yang300100/LifeLog/prototype/e2e_output/annotated_20260630_160411.png

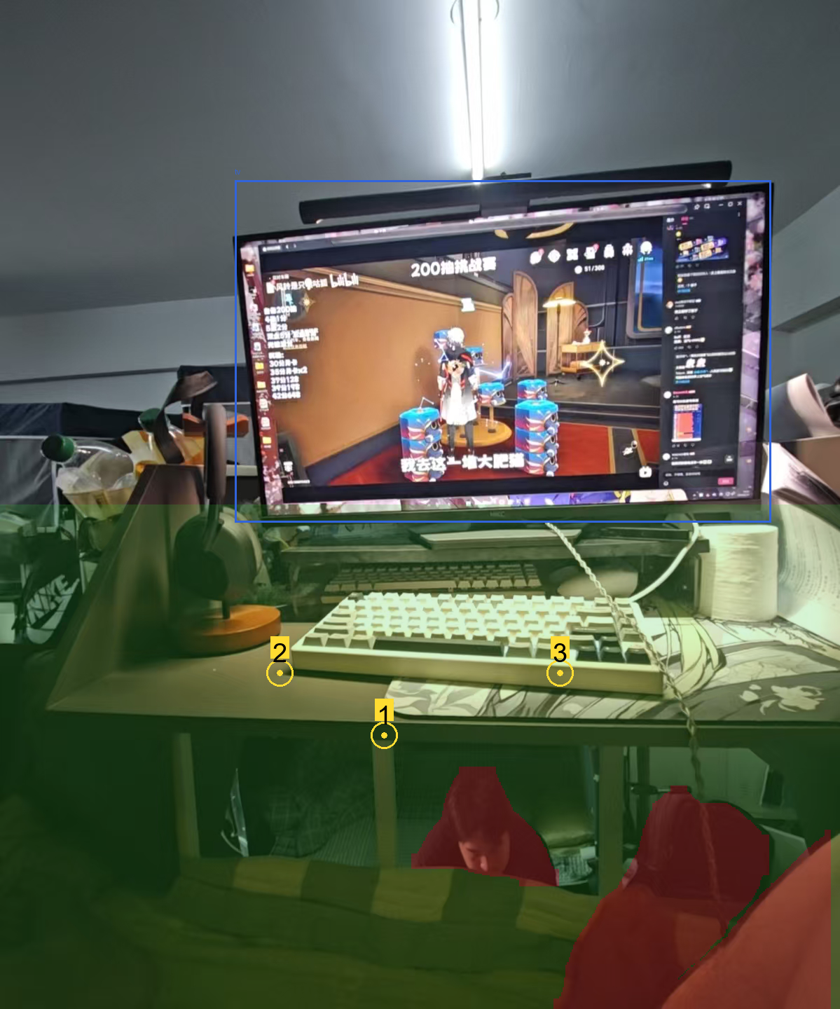
prototype/e2e_output/annotated_20260630_160411.png
