yang300100/LifeLog/prototype/output/01_character_raw.png

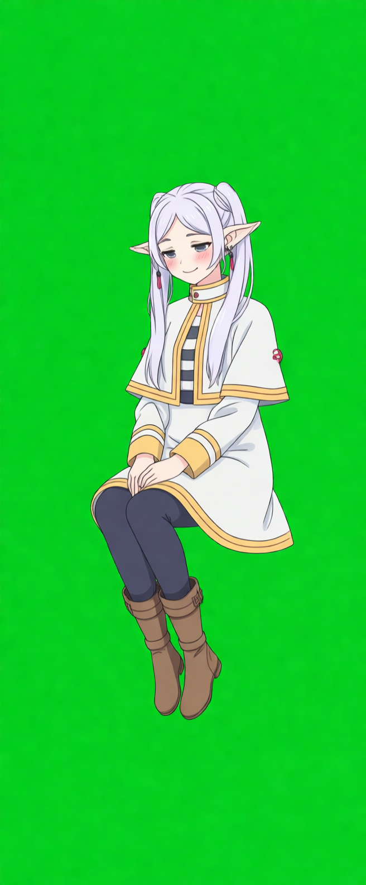
prototype/output/01_character_raw.png
