yang300100/LifeLog/prototype/output/02_character_nobg.png

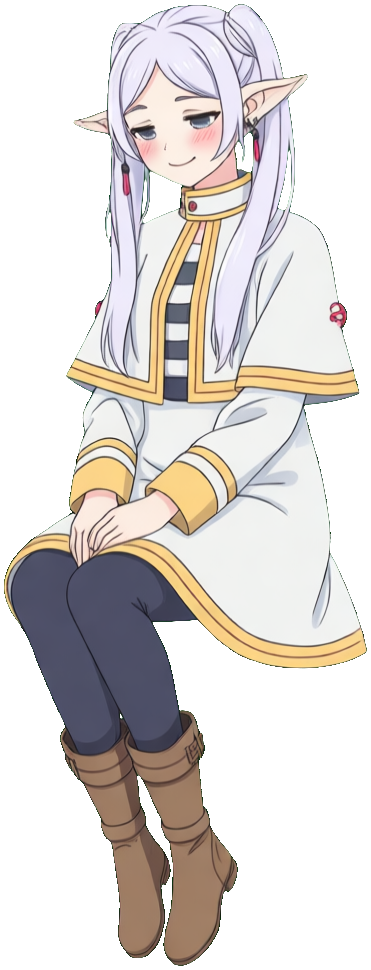
prototype/output/02_character_nobg.png
