yang300100/LifeLog/prototype/ref_01.png

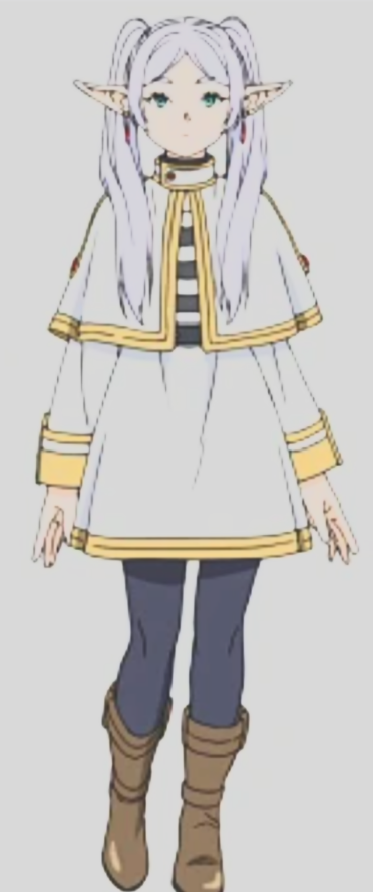
prototype/ref_01.png
