yang300100/LifeLog/prototype/seedream_output/showcase_A_standing_20260630_153909.png

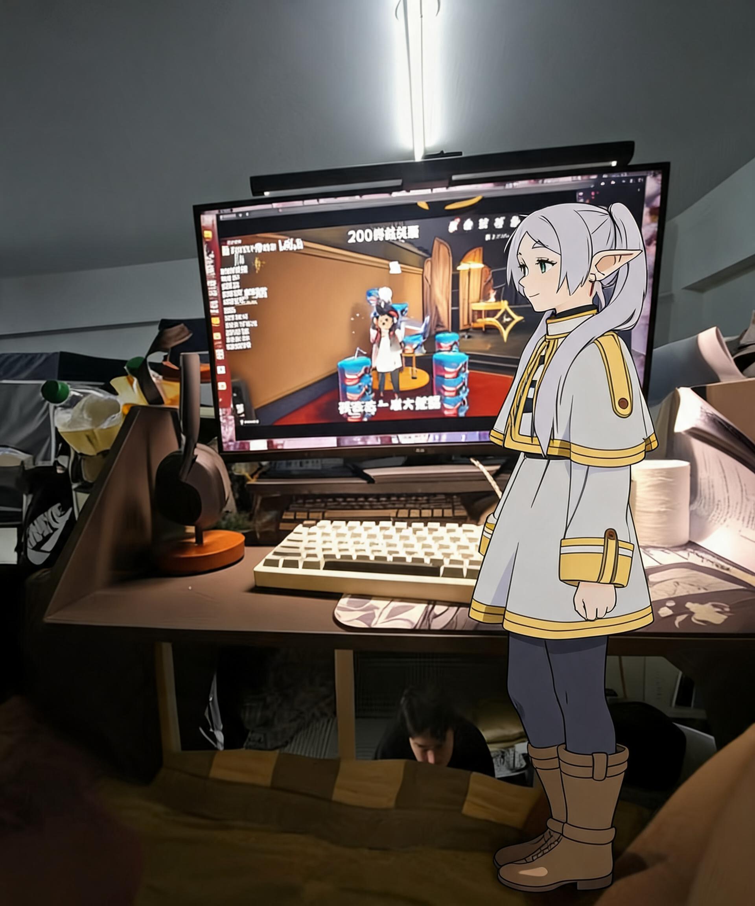
prototype/seedream_output/showcase_A_standing_20260630_153909.png
