yang300100/LifeLog/prototype/seedream_output/showcase_C_lean_forward_20260630_154052.png

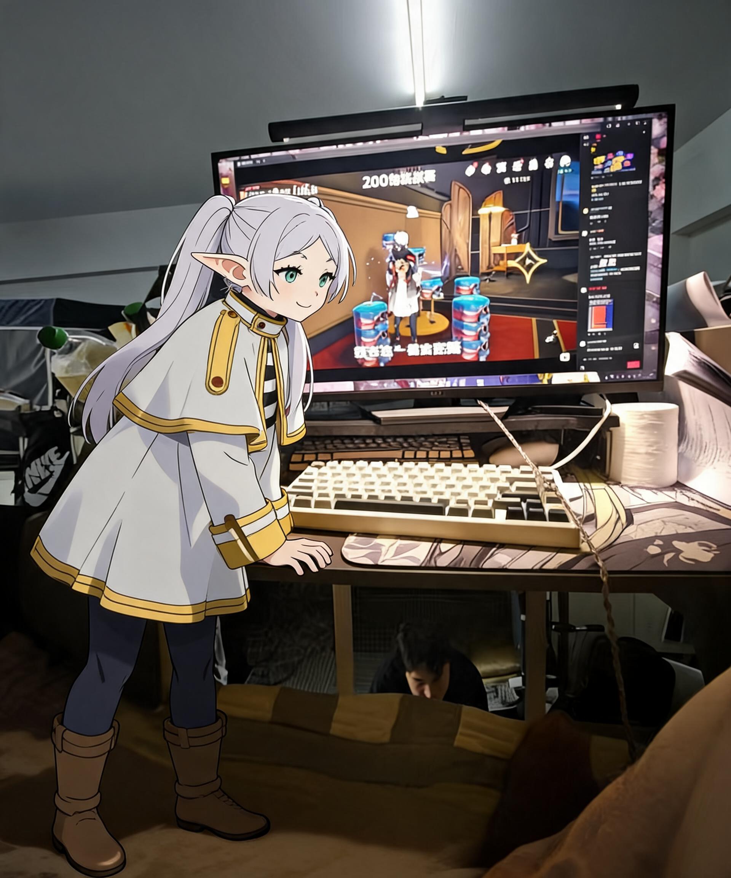
prototype/seedream_output/showcase_C_lean_forward_20260630_154052.png
