yang300100/LifeLog/prototype/e2e_output/final_result_20260630_160916.png

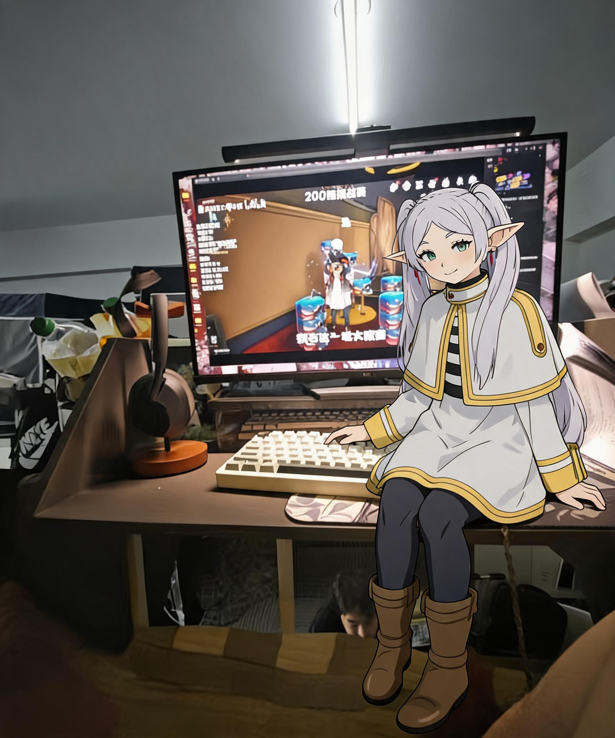
prototype/e2e_output/final_result_20260630_160916.png
