yang300100/LifeLog/prototype/test_scene.jpg

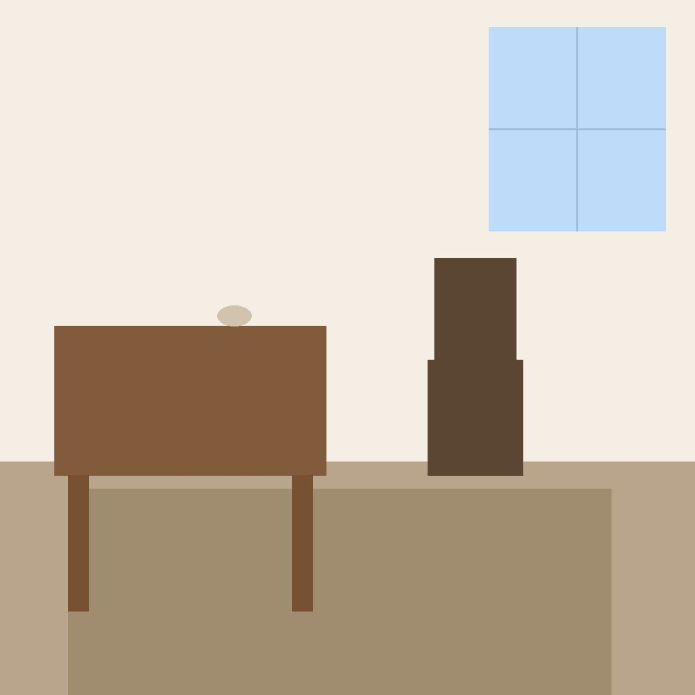
prototype/test_scene.jpg
