yang300100/LifeLog/firmware/lifelog/configuration.cpp

#include <Arduino.h>
#include "configuration.h"
#include "config.h"
#include "esp_camera.h"
#include <stdio.h>
#include <string.h>

// 简单的 key=value 解析，跳过空白和注释行
static bool parse_line(const char *line, char *key, size_t key_sz,
                       char *value, size_t val_sz) {
    const char *p = line;
    while (*p == ' ' || *p == '\t') p++;
    if (*p == '#' || *p == '\0' || *p == '\n' || *p == '\r') return false;

    const char *k = p;
    while (*p && *p != '=' && *p != '\n' && *p != '\r') p++;
    size_t klen = p - k;
    // 去掉 key 末尾的空格（"video_quality " → "video_quality"）
    while (klen > 0 && (k[klen - 1] == ' ' || k[klen - 1] == '\t')) klen--;
    if (klen >= key_sz) klen = key_sz - 1;
    memcpy(key, k, klen);
    key[klen] = '\0';

    if (*p != '=') return false;
    p++;

    while (*p == ' ' || *p == '\t') p++;
    const char *v = p;
    while (*p && *p != '\n' && *p != '\r') p++;
    size_t vlen = p - v;
    // 去掉 value 末尾的空格和回车
    while (vlen > 0 && (v[vlen - 1] == ' ' || v[vlen - 1] == '\t' || v[vlen - 1] == '\r')) vlen--;
    if (vlen >= val_sz) vlen = val_sz - 1;
    memcpy(value, v, vlen);
    value[vlen] = '\0';

    return true;
}

void config_set_defaults(AppConfig &cfg) {
    strcpy(cfg.capture_mode, "video");
    cfg.video_duration = VIDEO_DURATION_DEFAULT;
    cfg.video_resolution = VIDEO_RESOLUTION_DEFAULT;
    cfg.video_quality = VIDEO_QUALITY_DEFAULT;
    cfg.video_fps = VIDEO_FPS_DEFAULT;
    cfg.sharpness = 1;      // 默认锐度 +1
    cfg.contrast  = 0;      // 默认对比度中性
    cfg.saturation = 0;     // 默认饱和度中性
    cfg.interval = INTERVAL_DEFAULT;
    cfg.flash_threshold = FLASH_DARK_THRESHOLD;
    cfg.ble_advertise_timeout = BLE_ADV_TIMEOUT_DEFAULT;
    strcpy(cfg.ble_device_name, BLE_DEVICE_NAME_DEFAULT);
    cfg.ble_adv_interval = BLE_ADV_INTERVAL_DEFAULT;
}

bool config_load(const char *filepath, AppConfig &cfg) {
    config_set_defaults(cfg);

    FILE *f = fopen(filepath, "r");
    if (!f) return false;  // 文件不存在，使用默认值

    char line[128];
    char key[64], value[64];

    while (fgets(line, sizeof(line), f)) {
        // 检测行截断：最后字符不是 \n 且不是 EOF
        size_t len = strlen(line);
        if (len > 0 && line[len - 1] != '\n' && !feof(f)) {
            // 跳过被截断的行的剩余部分
            int c;
            while ((c = fgetc(f)) != '\n' && c != EOF) {}
            continue;
        }
        if (!parse_line(line, key, sizeof(key), value, sizeof(value)))
            continue;

        if (strcmp(key, "capture_mode") == 0) {
            strncpy(cfg.capture_mode, value, sizeof(cfg.capture_mode) - 1);
            cfg.capture_mode[sizeof(cfg.capture_mode) - 1] = '\0';  // strncpy 不保证 null 结尾
        }
        else if (strcmp(key, "video_duration") == 0) {
            cfg.video_duration = atoi(value);
            if (cfg.video_duration < 1000 || cfg.video_duration > 30000) {
                cfg.video_duration = VIDEO_DURATION_DEFAULT;
            }
        }
        else if (strcmp(key, "video_resolution") == 0) {
            if (strcmp(value, "QVGA") == 0) cfg.video_resolution = FRAMESIZE_QVGA;
            else if (strcmp(value, "VGA") == 0) cfg.video_resolution = FRAMESIZE_VGA;
            else if (strcmp(value, "SVGA") == 0) cfg.video_resolution = FRAMESIZE_SVGA;
            else if (strcmp(value, "XGA") == 0) cfg.video_resolution = FRAMESIZE_XGA;
            else if (strcmp(value, "SXGA") == 0) cfg.video_resolution = FRAMESIZE_SXGA;
            else if (strcmp(value, "UXGA") == 0) cfg.video_resolution = FRAMESIZE_UXGA;
            else if (strcmp(value, "QXGA") == 0) cfg.video_resolution = FRAMESIZE_QXGA;
        }
        else if (strcmp(key, "video_quality") == 0) {
            cfg.video_quality = atoi(value);
            if (cfg.video_quality < 10 || cfg.video_quality > 63) {
                cfg.video_quality = VIDEO_QUALITY_DEFAULT;
            }
        }
        else if (strcmp(key, "video_fps") == 0) {
            cfg.video_fps = atoi(value);
            // 防御性范围检查：fps 必须在 1-30 之间
            if (cfg.video_fps < 1 || cfg.video_fps > 30) {
                cfg.video_fps = VIDEO_FPS_DEFAULT;
            }
        }
        else if (strcmp(key, "sharpness") == 0) {
            cfg.sharpness = atoi(value);
            if (cfg.sharpness < -2 || cfg.sharpness > 2) cfg.sharpness = 0;
        }
        else if (strcmp(key, "contrast") == 0) {
            cfg.contrast = atoi(value);
            if (cfg.contrast < -2 || cfg.contrast > 2) cfg.contrast = 0;
        }
        else if (strcmp(key, "saturation") == 0) {
            cfg.saturation = atoi(value);
            if (cfg.saturation < -2 || cfg.saturation > 2) cfg.saturation = 0;
        }
        else if (strcmp(key, "interval") == 0) {
            cfg.interval = atoi(value);
            if (cfg.interval < 10000 || cfg.interval > 3600000) {
                cfg.interval = INTERVAL_DEFAULT;
            }
        }
        else if (strcmp(key, "flash_threshold") == 0) {
            cfg.flash_threshold = atoi(value);
            if (cfg.flash_threshold < 50 || cfg.flash_threshold > 500) {
                cfg.flash_threshold = FLASH_DARK_THRESHOLD;
            }
        }
        else if (strcmp(key, "ble_advertise_timeout") == 0) {
            cfg.ble_advertise_timeout = atoi(value);
            if (cfg.ble_advertise_timeout < 5000 || cfg.ble_advertise_timeout > 600000) {
                cfg.ble_advertise_timeout = BLE_ADV_TIMEOUT_DEFAULT;
            }
        }
        else if (strcmp(key, "ble_device_name") == 0) {
            strncpy(cfg.ble_device_name, value, sizeof(cfg.ble_device_name) - 1);
            cfg.ble_device_name[sizeof(cfg.ble_device_name) - 1] = '\0';
        }
        else if (strcmp(key, "ble_adv_interval") == 0) {
            cfg.ble_adv_interval = atoi(value);
            if (cfg.ble_adv_interval < 20 || cfg.ble_adv_interval > 1000) {
                cfg.ble_adv_interval = BLE_ADV_INTERVAL_DEFAULT;
            }
        }
    }

    fclose(f);
    return true;
}

bool config_save(const char *filepath, const AppConfig &cfg) {
    FILE *f = fopen(filepath, "w");
    if (!f) return false;

    fprintf(f, "# LifeLog Camera Configuration\n");
    fprintf(f, "capture_mode = %s\n", cfg.capture_mode);
    fprintf(f, "video_duration = %u\n", cfg.video_duration);
    fprintf(f, "video_resolution = %s\n",
            cfg.video_resolution == FRAMESIZE_QVGA ? "QVGA" :
            cfg.video_resolution == FRAMESIZE_VGA  ? "VGA"  :
            cfg.video_resolution == FRAMESIZE_SVGA ? "SVGA" :
            cfg.video_resolution == FRAMESIZE_XGA  ? "XGA"  :
            cfg.video_resolution == FRAMESIZE_SXGA ? "SXGA" :
            cfg.video_resolution == FRAMESIZE_UXGA ? "UXGA" : "QXGA");
    fprintf(f, "video_quality = %u\n", cfg.video_quality);
    fprintf(f, "video_fps = %u\n", cfg.video_fps);
    fprintf(f, "sharpness = %d\n", (int)cfg.sharpness);
    fprintf(f, "contrast = %d\n", (int)cfg.contrast);
    fprintf(f, "saturation = %d\n", (int)cfg.saturation);
    fprintf(f, "interval = %u\n", cfg.interval);
    fprintf(f, "flash_threshold = %u\n", cfg.flash_threshold);
    fprintf(f, "ble_advertise_timeout = %u\n", cfg.ble_advertise_timeout);
    fprintf(f, "ble_device_name = %s\n", cfg.ble_device_name);
    fprintf(f, "ble_adv_interval = %u\n", cfg.ble_adv_interval);

    fclose(f);
    return true;
}
