yang300100/LifeLog/prototype/test_real_scene.jpg

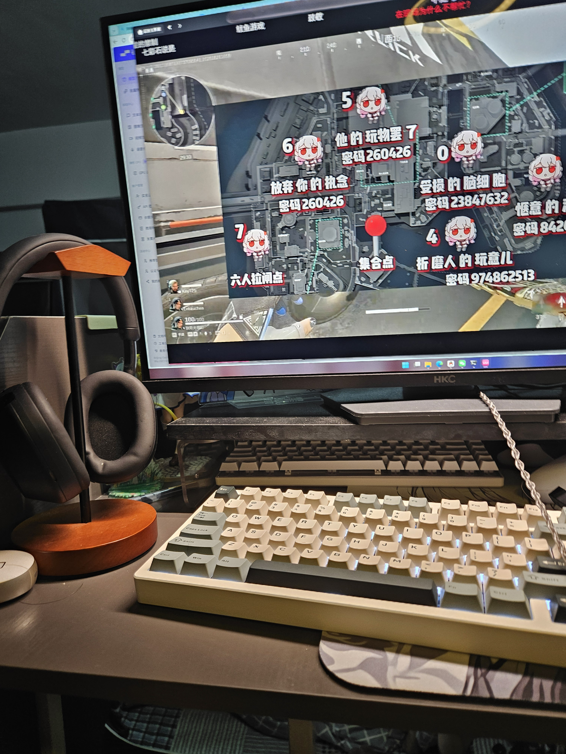
prototype/test_real_scene.jpg
